LuzPlazas/FermentadorCafe/MF-A002-V1/MF-P008.SLDPRT

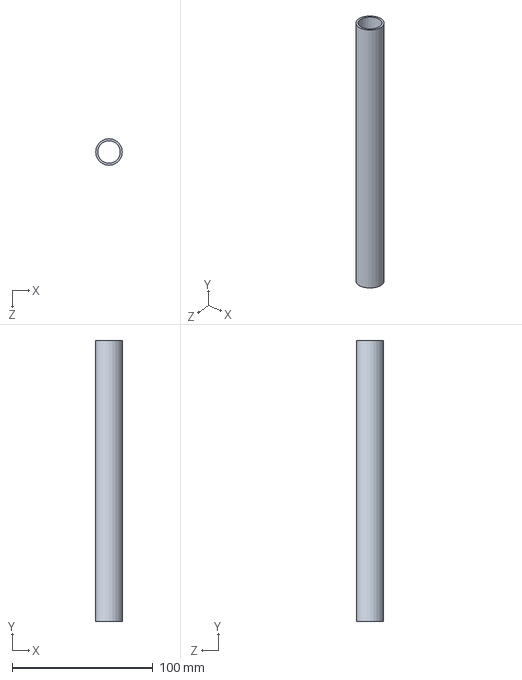
[picture p15: CAD file, 2023-03-03]
MF-A002-V1/MF-P008.SLDPRT
19.0 x 200.0 x 19.0 mm
