LuzPlazas/FermentadorCafe/MF-A002-V1/MF-P013-v2.SLDPRT

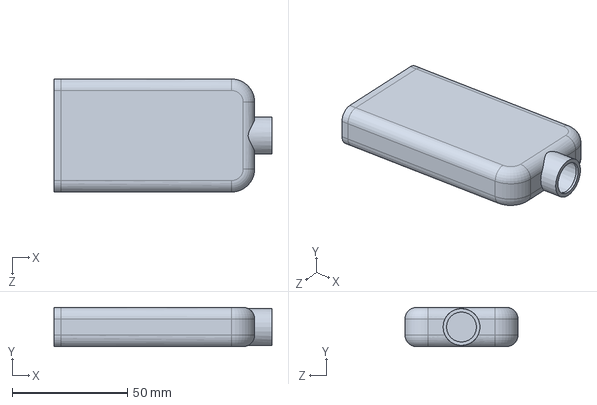
[picture p16: CAD file, 2023-03-03]
MF-A002-V1/MF-P013-v2.SLDPRT
94.5 x 17.0 x 49.0 mm
