LuzPlazas/FermentadorCafe/MF-A002-V1/Imprimir/Part5.STL

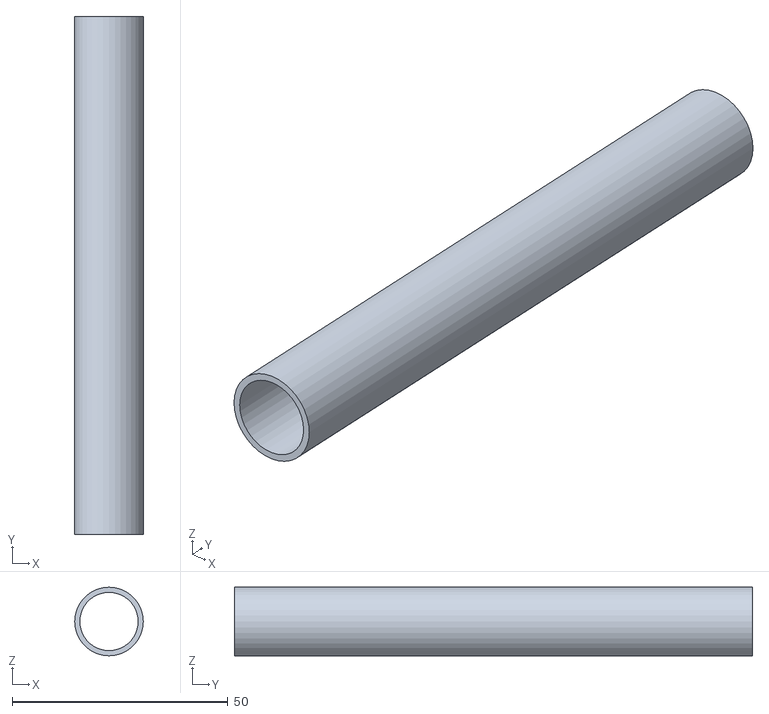
[picture p17: CAD file, 2023-03-03]
MF-A002-V1/Imprimir/Part5.STL
15.9 x 120.0 x 15.9
