LuzPlazas/FermentadorCafe/MF-A002-V1/MF-P014.SLDPRT

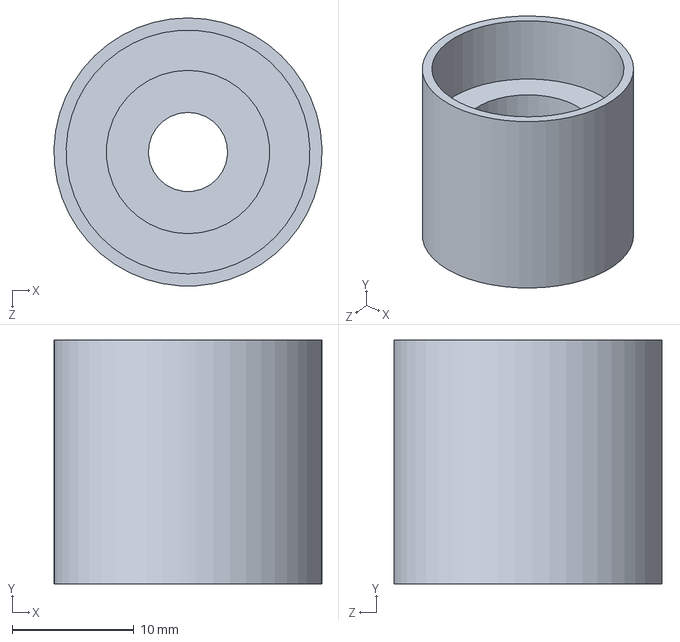
[picture p18: CAD file, 2023-03-03]
MF-A002-V1/MF-P014.SLDPRT
22.0 x 20.0 x 22.0 mm
