LuzPlazas/FermentadorCafe/MF-A002-V1/MF-P015.SLDPRT

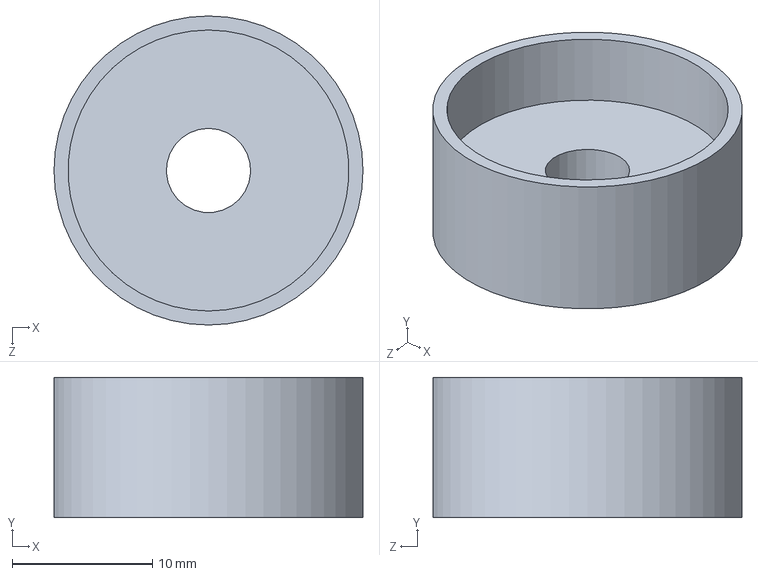
[picture p19: CAD file, 2023-03-03]
MF-A002-V1/MF-P015.SLDPRT
22.0 x 10.0 x 22.0 mm
