LuzPlazas/FermentadorCafe/MF-A002-V1/MF-P021.SLDPRT

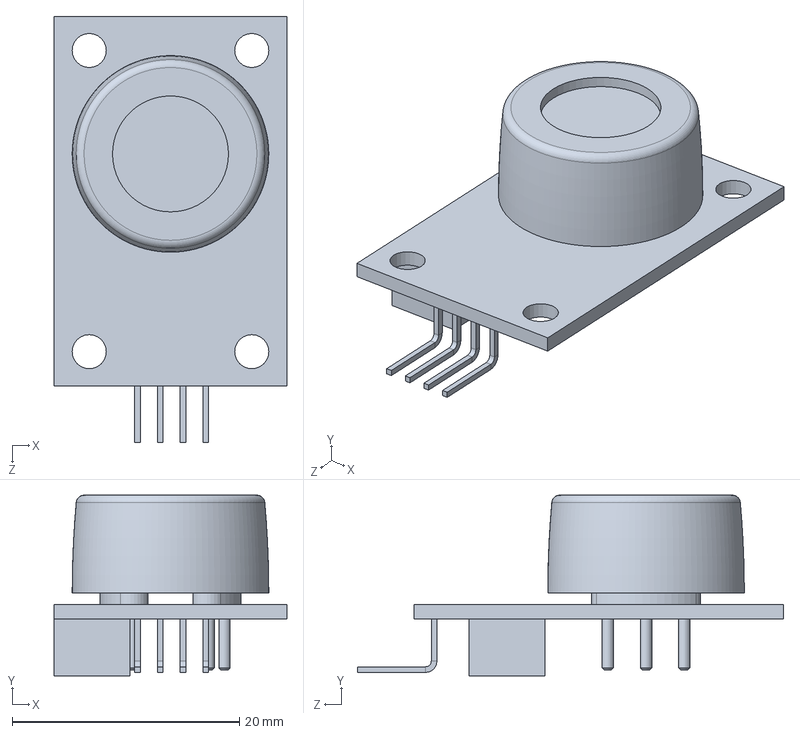
[picture p20: CAD file, 2023-03-03]
MF-A002-V1/MF-P021.SLDPRT
20.5 x 15.9 x 37.5 mm
