LuzPlazas/FermentadorCafe/MF-A002-V1/Part6.SLDPRT

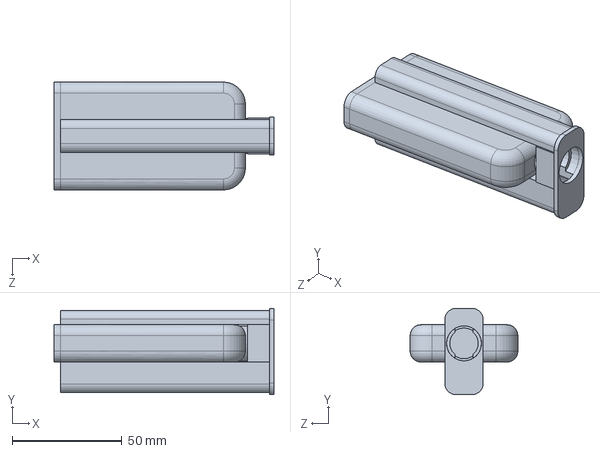
[picture p21: CAD file, 2023-03-03]
MF-A002-V1/Part6.SLDPRT
100.0 x 39.3 x 49.0 mm
