LuzPlazas/FermentadorCafe/MF-A002-V1/lock.SLDPRT

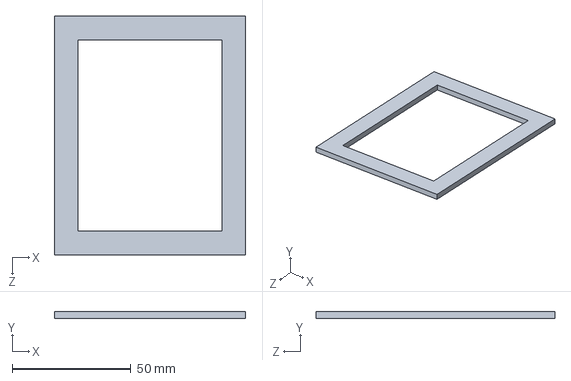
[picture p22: CAD file, 2023-03-03]
MF-A002-V1/lock.SLDPRT
80.5 x 3.00 x 100.5 mm
