LuzPlazas/FermentadorCafe/MF-A002-V1/MF-P020.SLDPRT

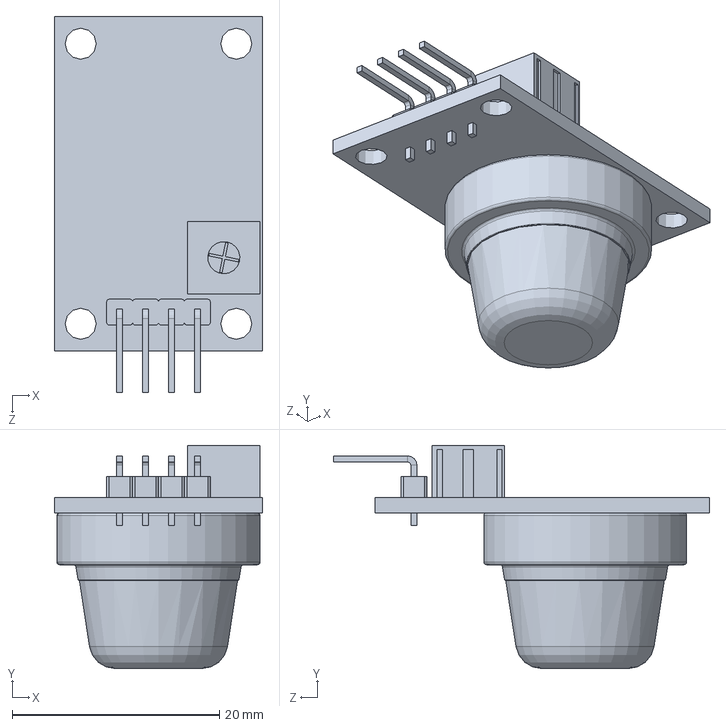
[picture p23: CAD file, 2023-03-03]
MF-A002-V1/MF-P020.SLDPRT
20.1 x 21.5 x 36.2 mm
