LuzPlazas/FermentadorCafe/MF-A002-V1/MF-P010.SLDPRT

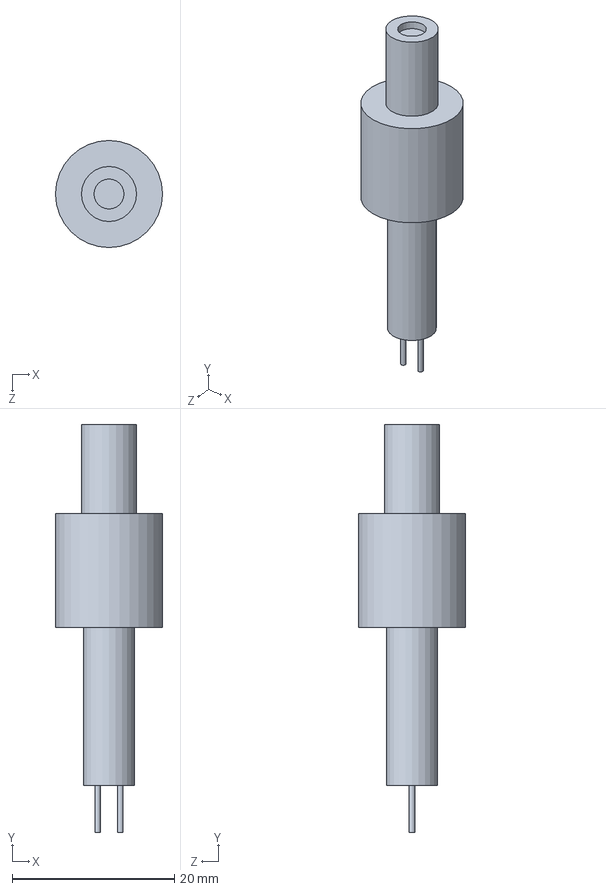
[picture p24: CAD file, 2023-03-03]
MF-A002-V1/MF-P010.SLDPRT
13.2 x 50.3 x 13.2 mm
