LuzPlazas/FermentadorCafe/MF-A002-V1/Part1.SLDPRT

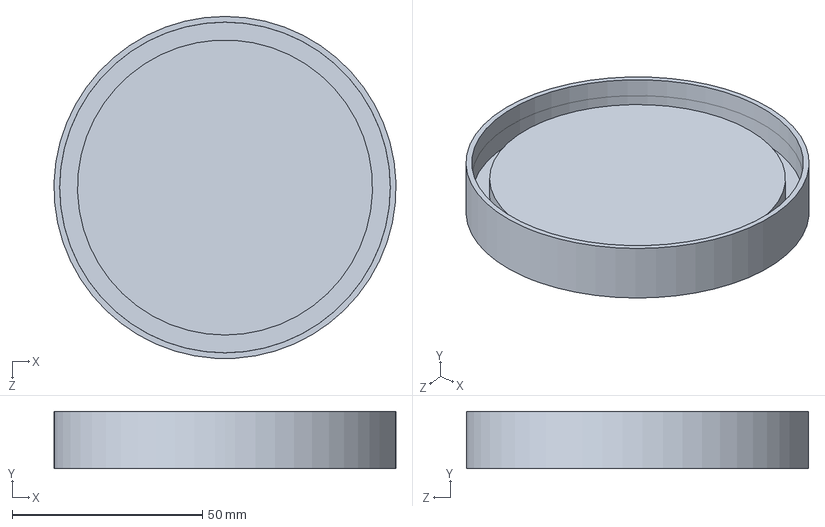
[picture p25: CAD file, 2023-03-03]
MF-A002-V1/Part1.SLDPRT
90.0 x 15.0 x 90.0 mm
