LuzPlazas/FermentadorCafe/MF-A002-V1/MF-P019b.SLDPRT

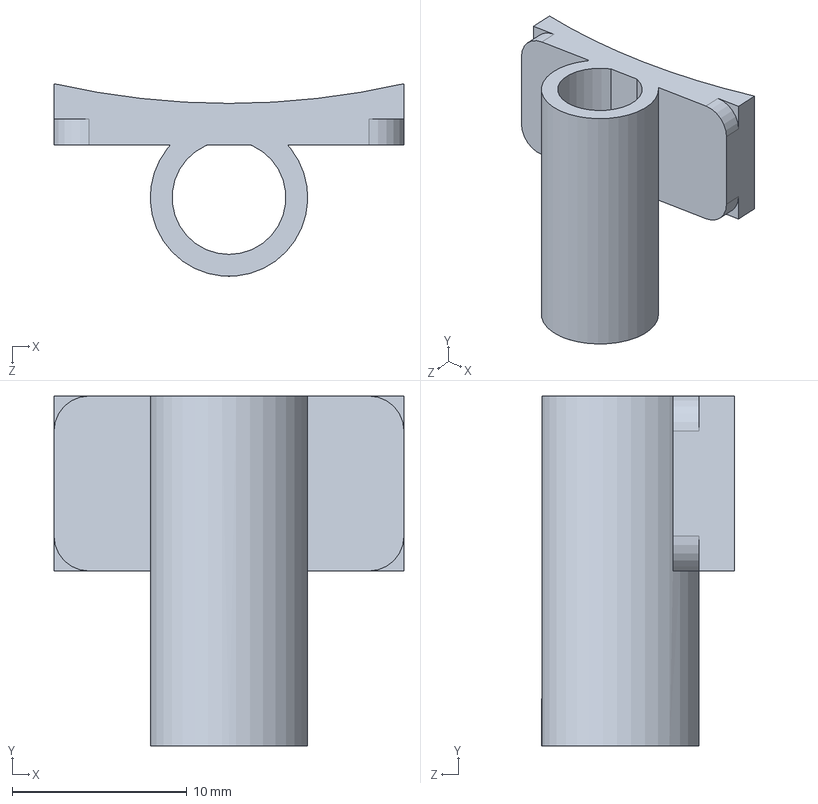
[picture p26: CAD file, 2023-03-03]
MF-A002-V1/MF-P019b.SLDPRT
20.0 x 20.0 x 11.0 mm
