LuzPlazas/FermentadorCafe/MF-A002-V1/MF-P012.SLDPRT

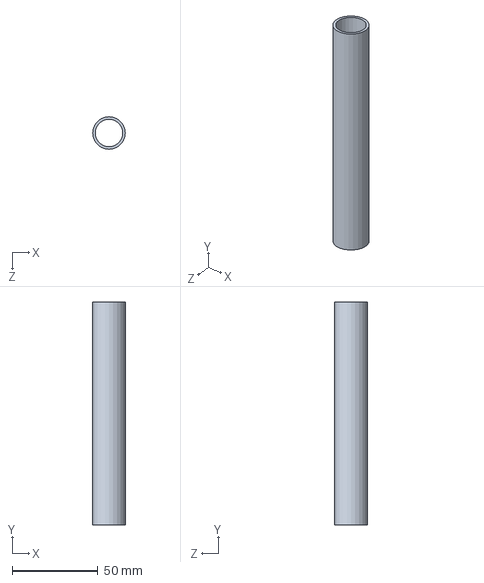
[picture p27: CAD file, 2023-03-03]
MF-A002-V1/MF-P012.SLDPRT
19.0 x 130.0 x 19.0 mm
