LuzPlazas/FermentadorCafe/MF-A002-V1/right.SLDPRT

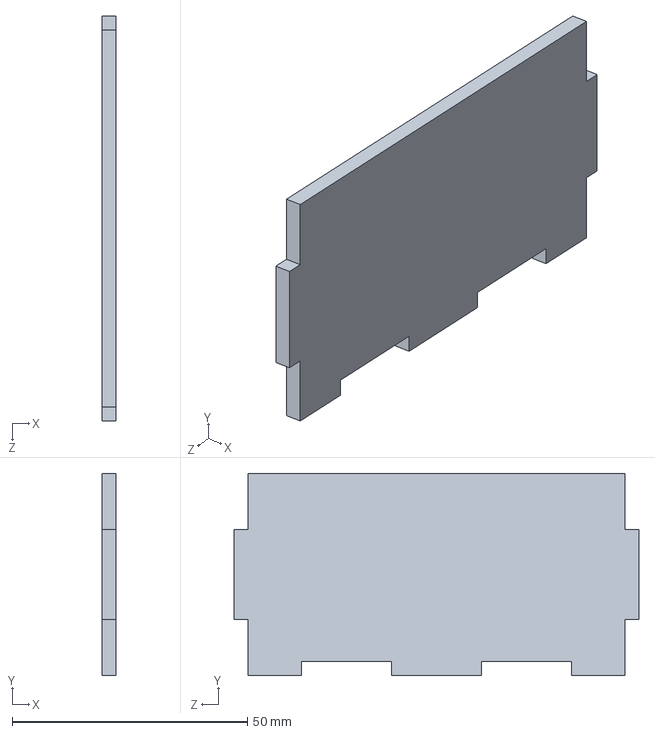
[picture p28: CAD file, 2023-03-03]
MF-A002-V1/right.SLDPRT
3.00 x 43.0 x 86.0 mm
