LuzPlazas/FermentadorCafe/MF-A002-V1/MF-P019.SLDPRT

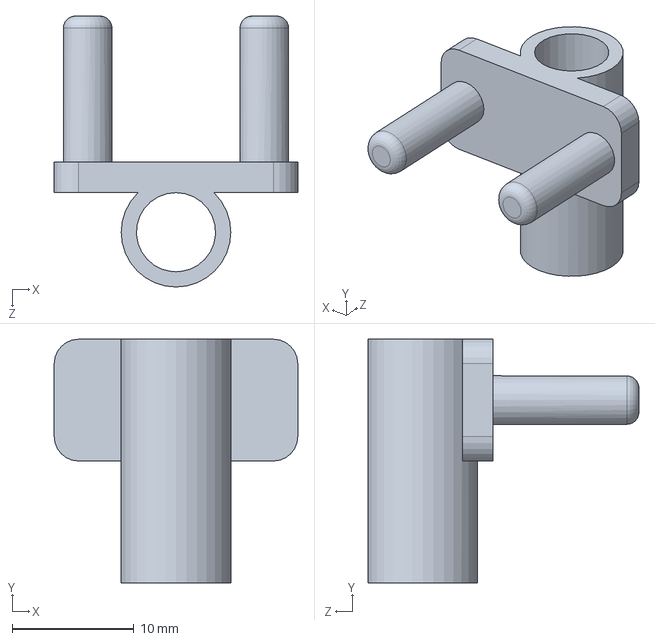
[picture p29: CAD file, 2023-03-03]
MF-A002-V1/MF-P019.SLDPRT
20.0 x 20.0 x 22.2 mm
