LuzPlazas/FermentadorCafe/MF-A002-V1/e1.SLDPRT

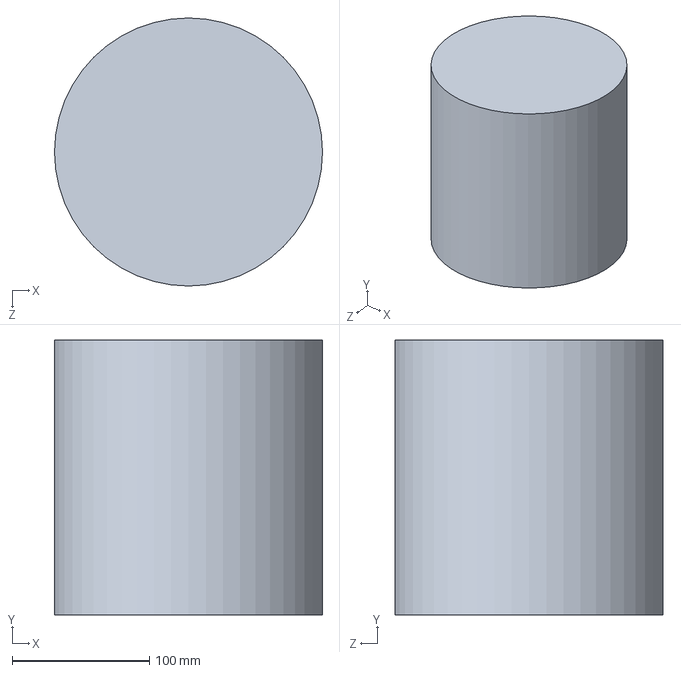
[picture p30: CAD file, 2023-03-03]
MF-A002-V1/e1.SLDPRT
195.0 x 200.0 x 195.0 mm
