LuzPlazas/FermentadorCafe/MF-A002-V1/botom.SLDPRT

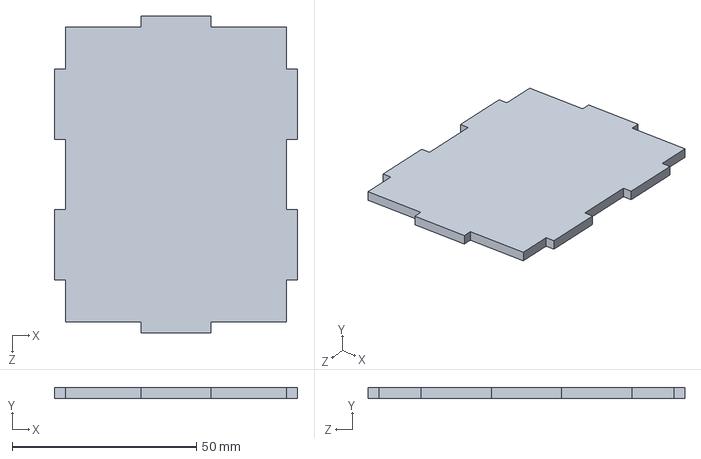
[picture p31: CAD file, 2023-03-03]
MF-A002-V1/botom.SLDPRT
66.0 x 3.00 x 86.0 mm
