LuzPlazas/FermentadorCafe/MF-A002-V1/MF-P009.SLDPRT

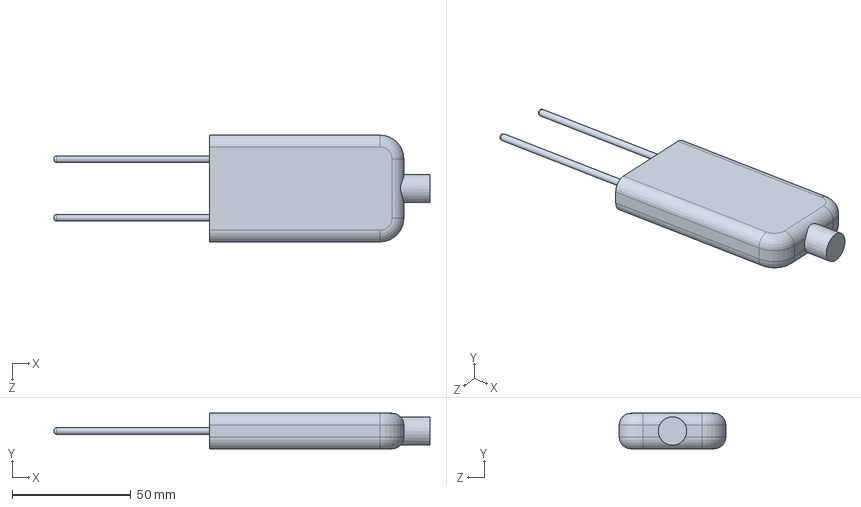
[picture p32: CAD file, 2023-03-03]
MF-A002-V1/MF-P009.SLDPRT
158.5 x 15.0 x 45.0 mm
