LuzPlazas/FermentadorCafe/MF-A002-V1/tapa.SLDPRT

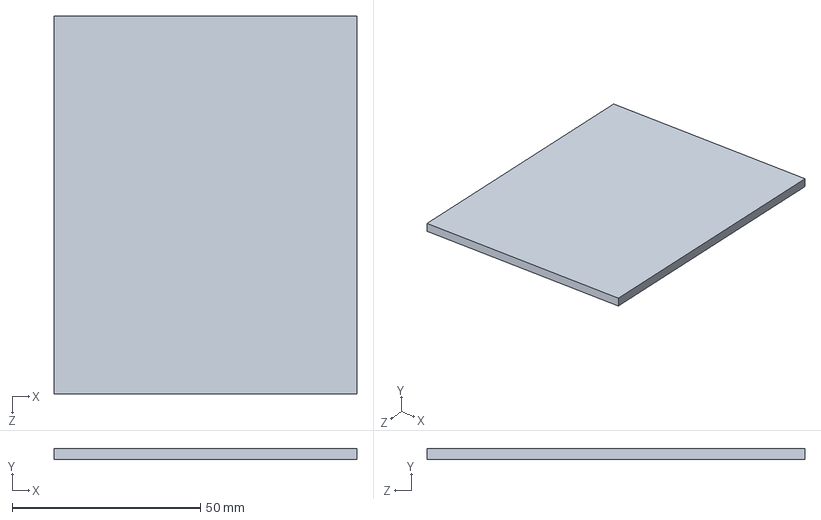
[picture p33: CAD file, 2023-03-03]
MF-A002-V1/tapa.SLDPRT
80.5 x 3.00 x 100.5 mm
