LuzPlazas/FermentadorCafe/MF-A002-V1/Part2.SLDPRT

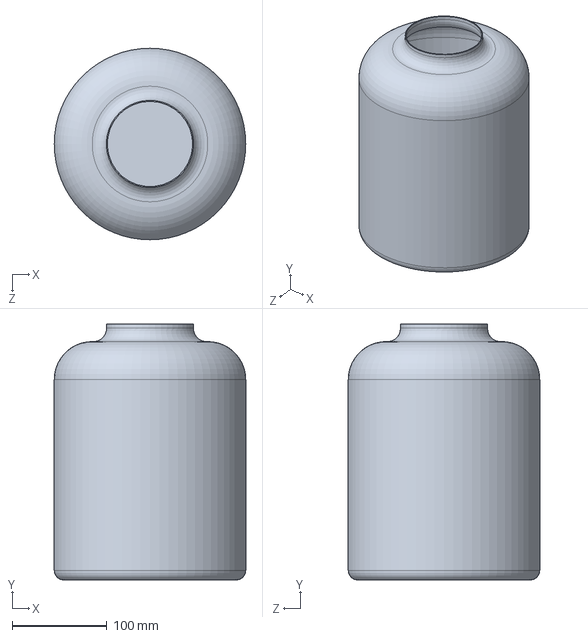
[picture p34: CAD file, 2023-03-03]
MF-A002-V1/Part2.SLDPRT
202.0 x 270.0 x 202.0 mm
